Pacane/pacino/variants/insert_test.3mf

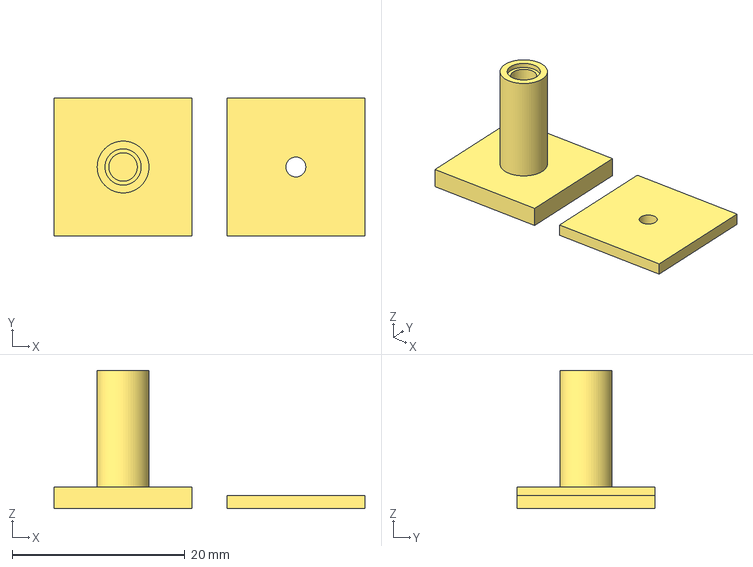
[picture p42: CAD file, 2026-09-14]
variants/insert_test.3mf
36.0 x 16.0 x 16.0 mm
