Pacane/pacino/variants/5col_extra2_bat103450_nodisplay/plate_right.step

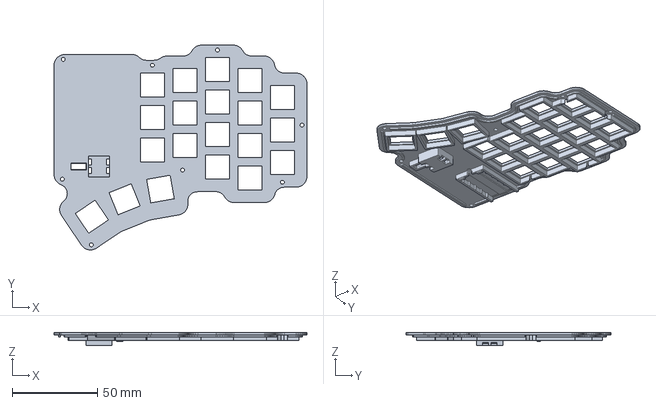
[picture p44: CAD file, 2026-09-14]
variants/5col_extra2_bat103450_nodisplay/plate_right.step
148.3 x 120.1 x 7.50 mm
