Pacane/pacino/variants/5col_extra2_bat303040_pcb_flat/pcb_test.3mf

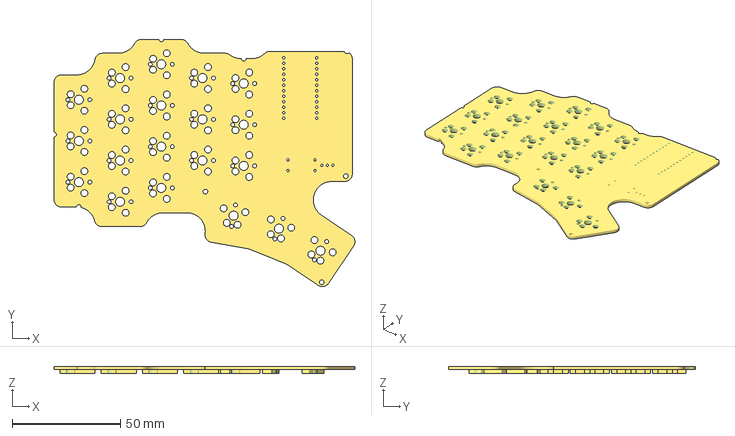
[picture p45: CAD file, 2026-09-14]
variants/5col_extra2_bat303040_pcb_flat/pcb_test.3mf
139.1 x 114.3 x 3.45 mm
