Pacane/pacino/variants/5col_extra2_bat902030_display/plate_right.step

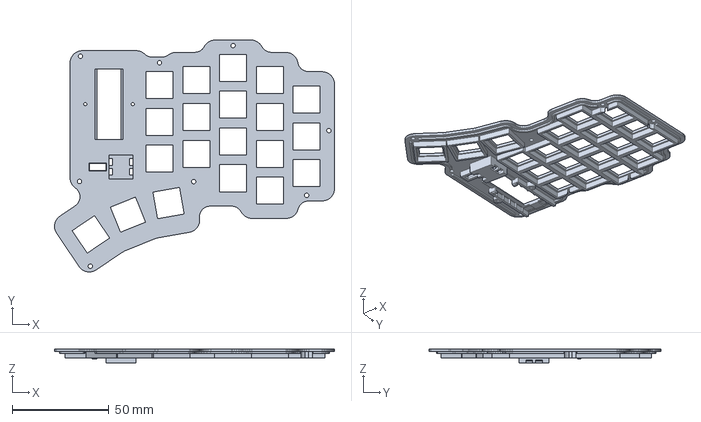
[picture p46: CAD file, 2026-09-14]
variants/5col_extra2_bat902030_display/plate_right.step
144.9 x 120.1 x 7.50 mm
