Pacane/pacino/variants/5col_extra2_bat902030_pcb_pod/plate_left.step

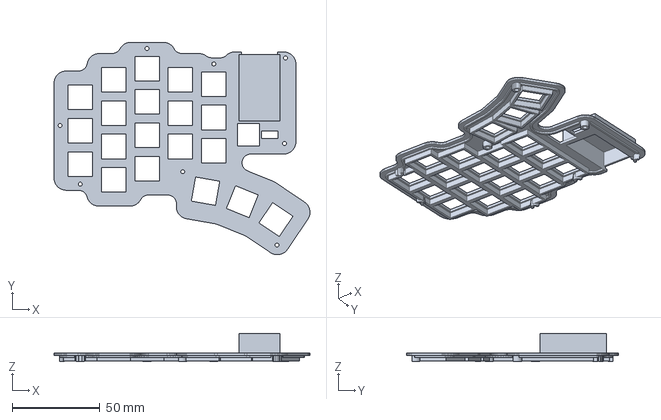
[picture p47: CAD file, 2026-09-14]
variants/5col_extra2_bat902030_pcb_pod/plate_left.step
146.1 x 121.3 x 16.1 mm
