Pacane/pacino/variants/5col_noextra_bat103450_display/bezel_left.step

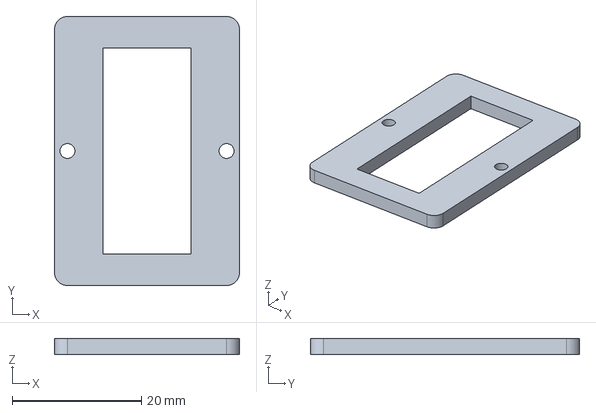
[picture p48: CAD file, 2026-09-14]
variants/5col_noextra_bat103450_display/bezel_left.step
28.6 x 41.6 x 2.50 mm
