Pacane/pacino/variants/5col_noextra_bat103450_nodisplay/plate_left.step

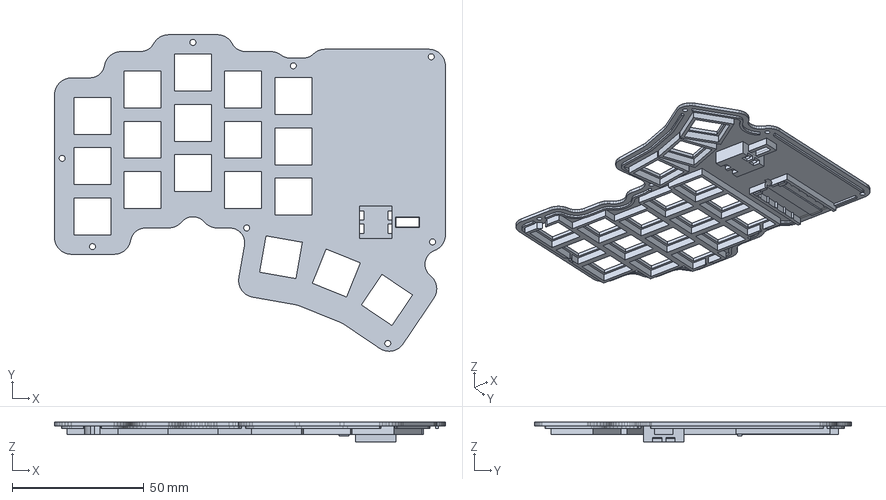
[picture p49: CAD file, 2026-09-14]
variants/5col_noextra_bat103450_nodisplay/plate_left.step
148.3 x 120.1 x 7.50 mm
