Pacane/pacino/variants/5col_noextra_bat902030_nodisplay/plate_right.step

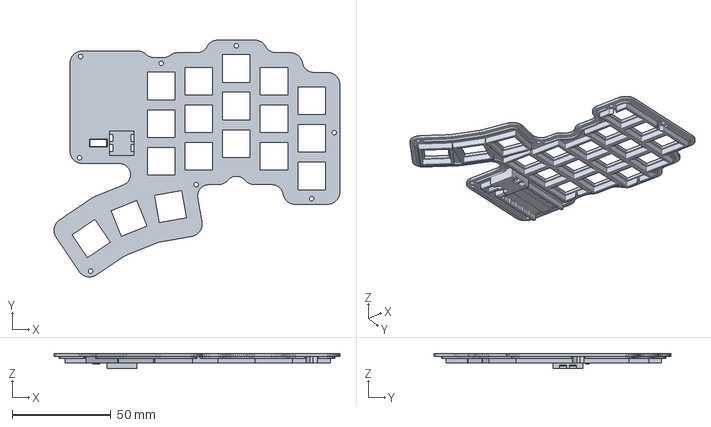
[picture p50: CAD file, 2026-09-14]
variants/5col_noextra_bat902030_nodisplay/plate_right.step
144.9 x 120.1 x 7.50 mm
