Pacane/pacino/variants/6col_extra2_bat902030_display/plate_right.step

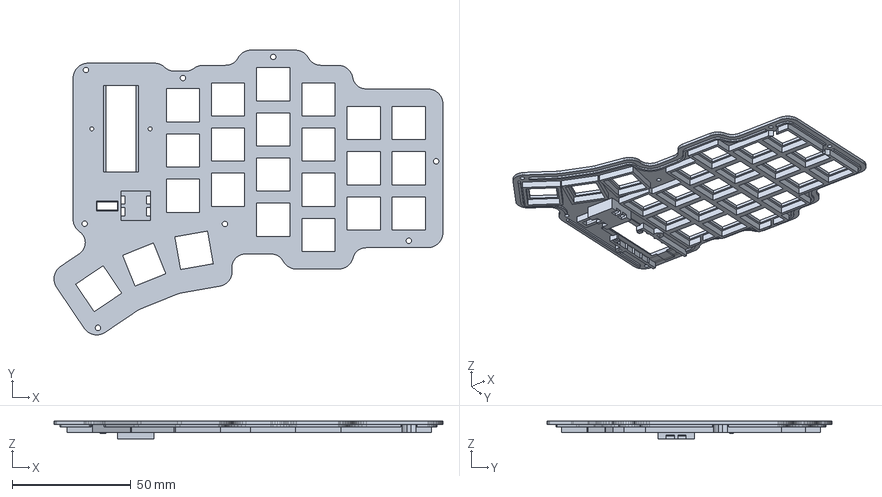
[picture p52: CAD file, 2026-09-14]
variants/6col_extra2_bat902030_display/plate_right.step
164.0 x 120.1 x 7.50 mm
