Pacane/pacino/variants/6col_noextra_bat902030_nodisplay/plate_right.step

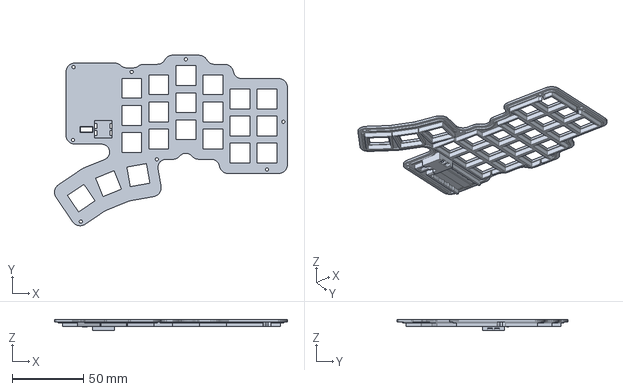
[picture p54: CAD file, 2026-09-14]
variants/6col_noextra_bat902030_nodisplay/plate_right.step
164.0 x 120.1 x 7.50 mm
