Pacane/pacino/variants/5col_extra2_bat303040_pcb_flat/plate_right.step

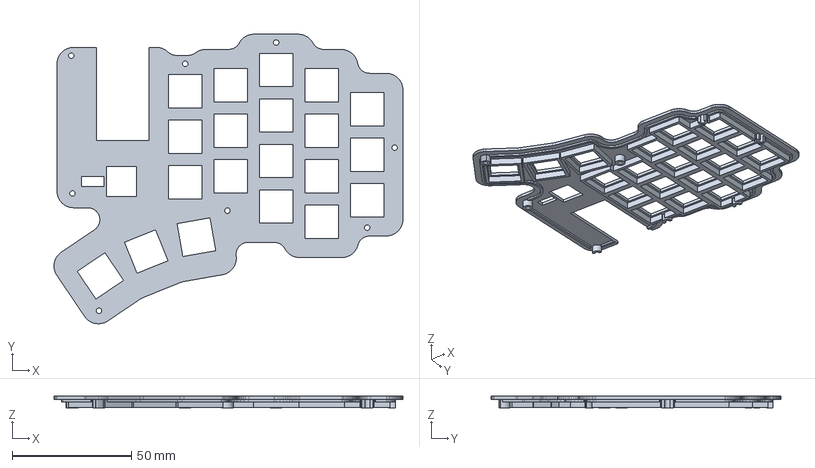
[picture p55: CAD file, 2026-09-14]
variants/5col_extra2_bat303040_pcb_flat/plate_right.step
146.1 x 121.3 x 5.00 mm
