Pacane/pacino/variants/5col_extra2_bat902030_pcb_pod/pcb_test.3mf

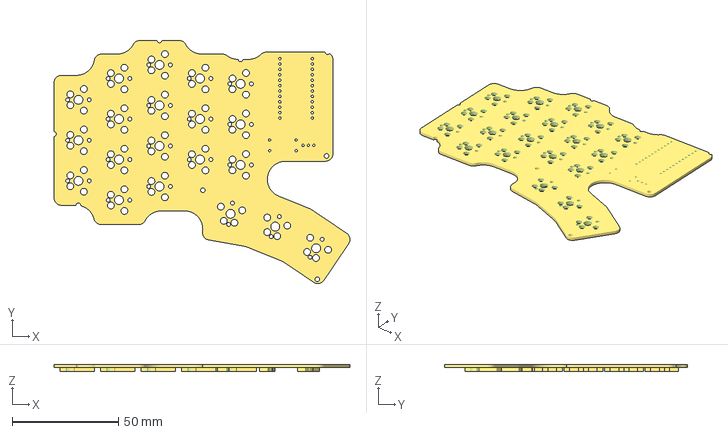
[picture p56: CAD file, 2026-09-14]
variants/5col_extra2_bat902030_pcb_pod/pcb_test.3mf
139.1 x 114.3 x 3.45 mm
