Pacane/pacino/variants/6col_noextra_bat103450_display/plate_left.step

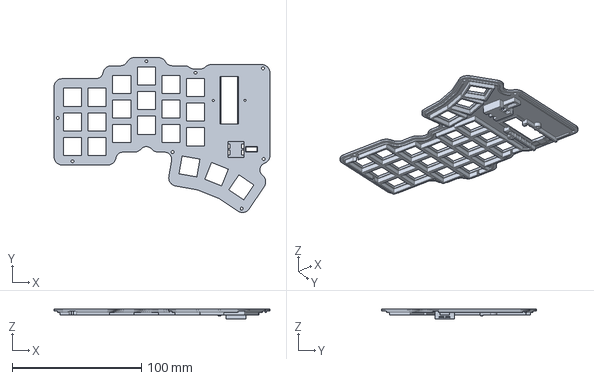
[picture p57: CAD file, 2026-09-14]
variants/6col_noextra_bat103450_display/plate_left.step
167.4 x 120.1 x 7.50 mm
