Pacane/pacino/variants/5col_extra2_bat103450_display/preview_assembly.png

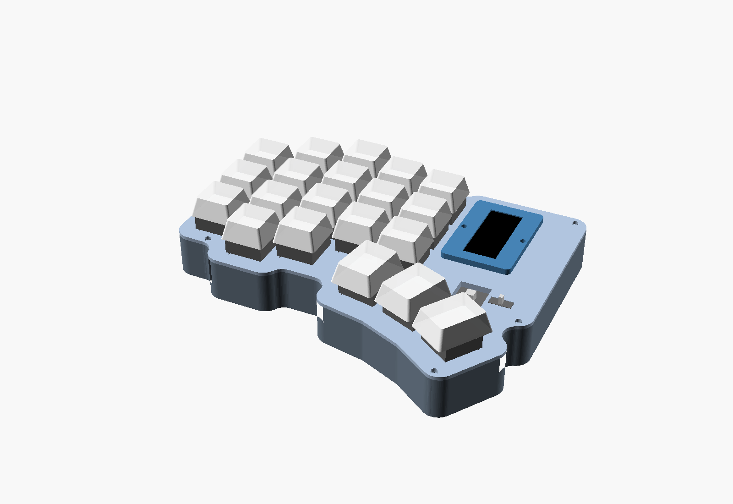
variants/5col_extra2_bat103450_display/preview_assembly.png
