Pacane/pacino/variants/5col_extra2_bat103450_display/wiring_guide.png

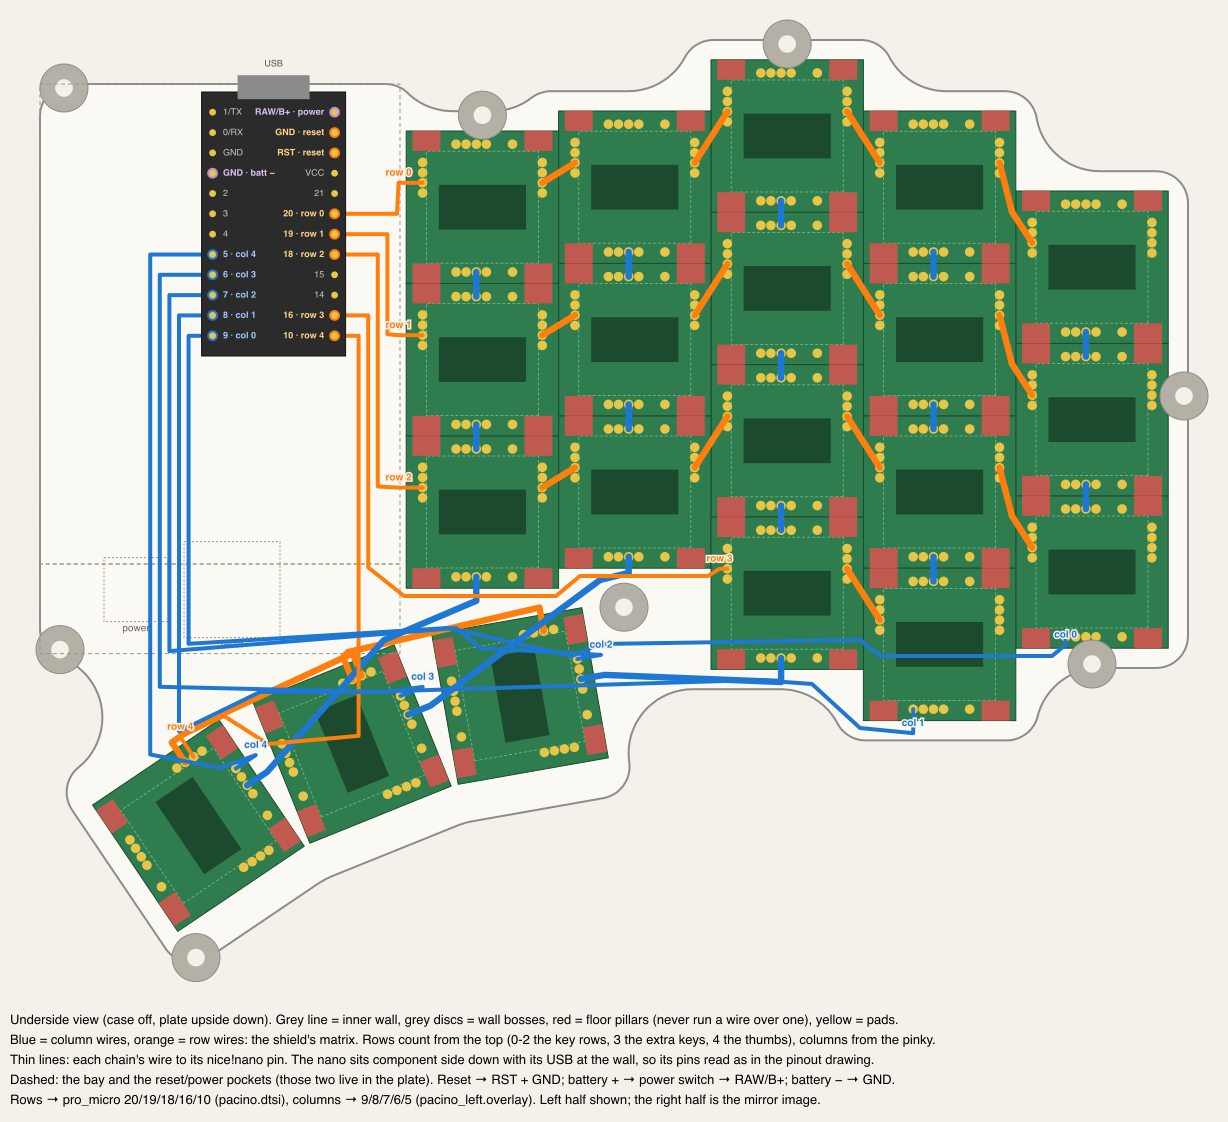
variants/5col_extra2_bat103450_display/wiring_guide.png
