Pacane/pacino/variants/5col_extra2_bat902030_display/preview_assembly.png

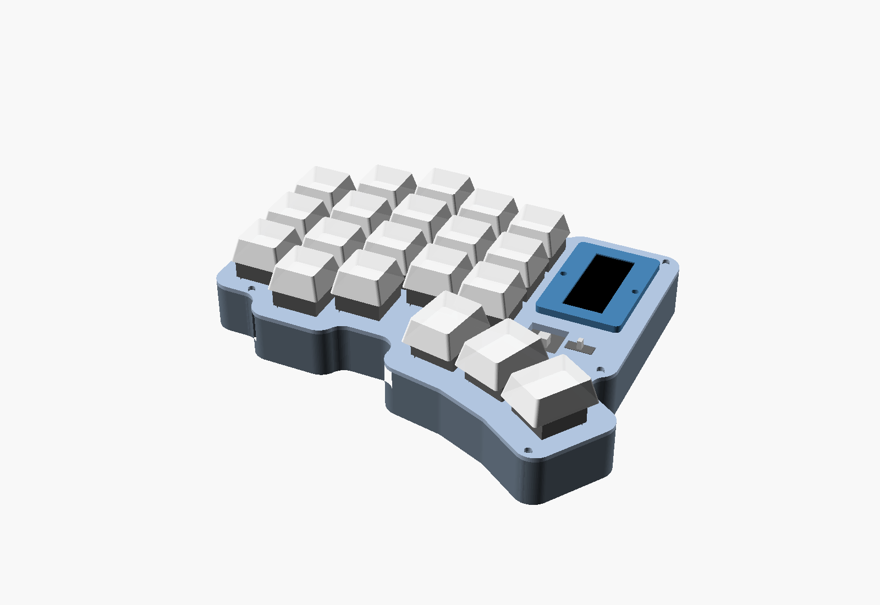
variants/5col_extra2_bat902030_display/preview_assembly.png
