Pacane/pacino/variants/5col_extra2_bat902030_pcb_pod/preview_assembly.png

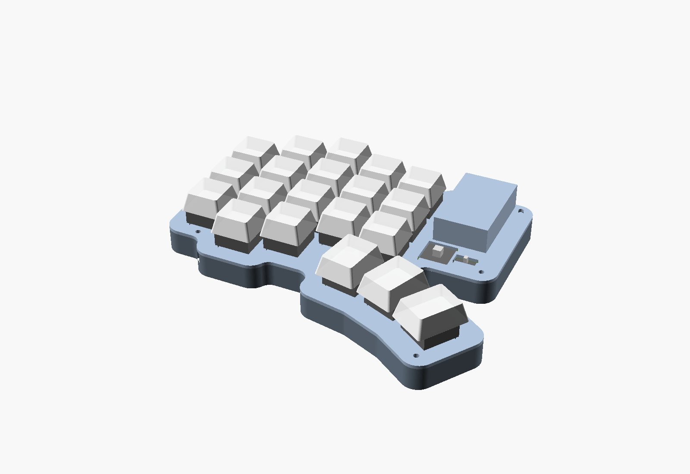
variants/5col_extra2_bat902030_pcb_pod/preview_assembly.png
