Pacane/pacino/variants/6col_extra2_bat103450_display/preview_assembly.png

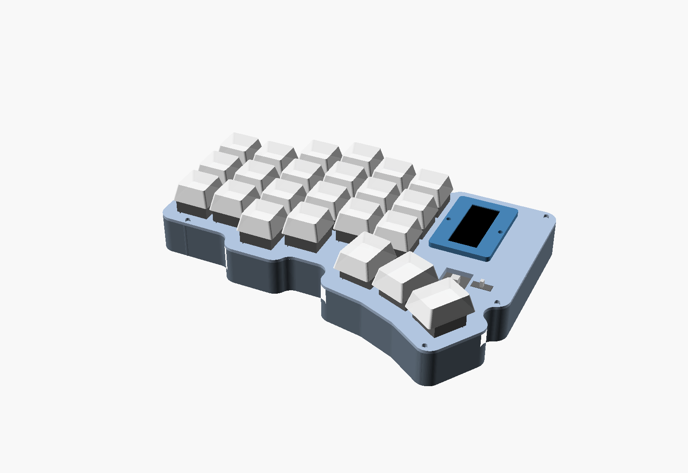
variants/6col_extra2_bat103450_display/preview_assembly.png
