Pacane/pacino/variants/6col_extra2_bat103450_display/wiring_guide.png

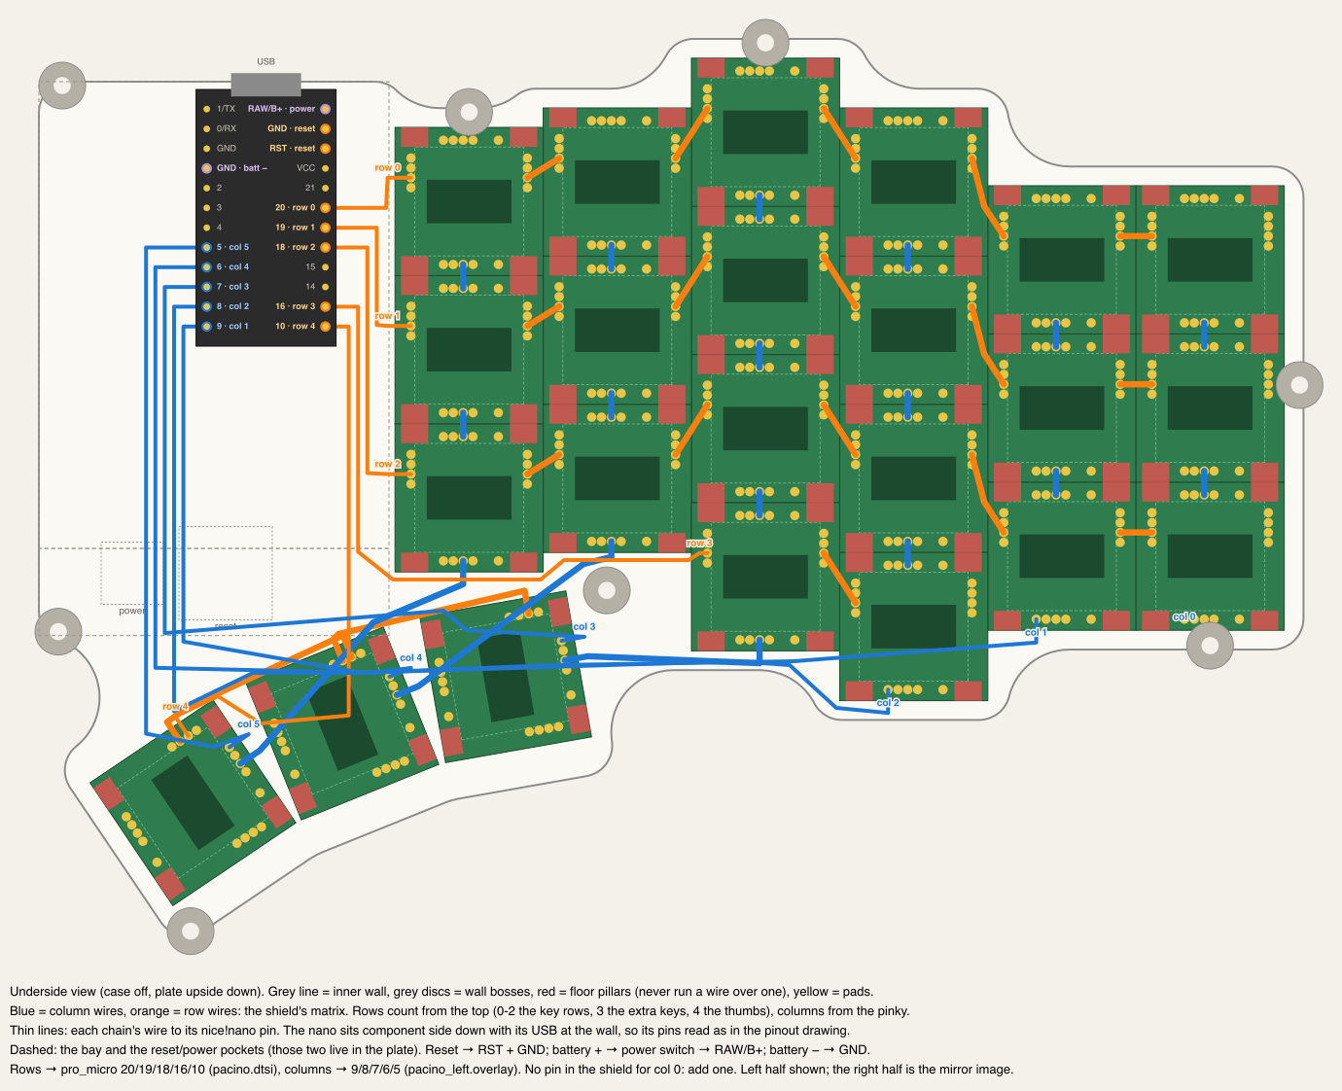
variants/6col_extra2_bat103450_display/wiring_guide.png
