Pacane/pacino/variants/6col_extra2_bat902030_display/wiring_guide.png

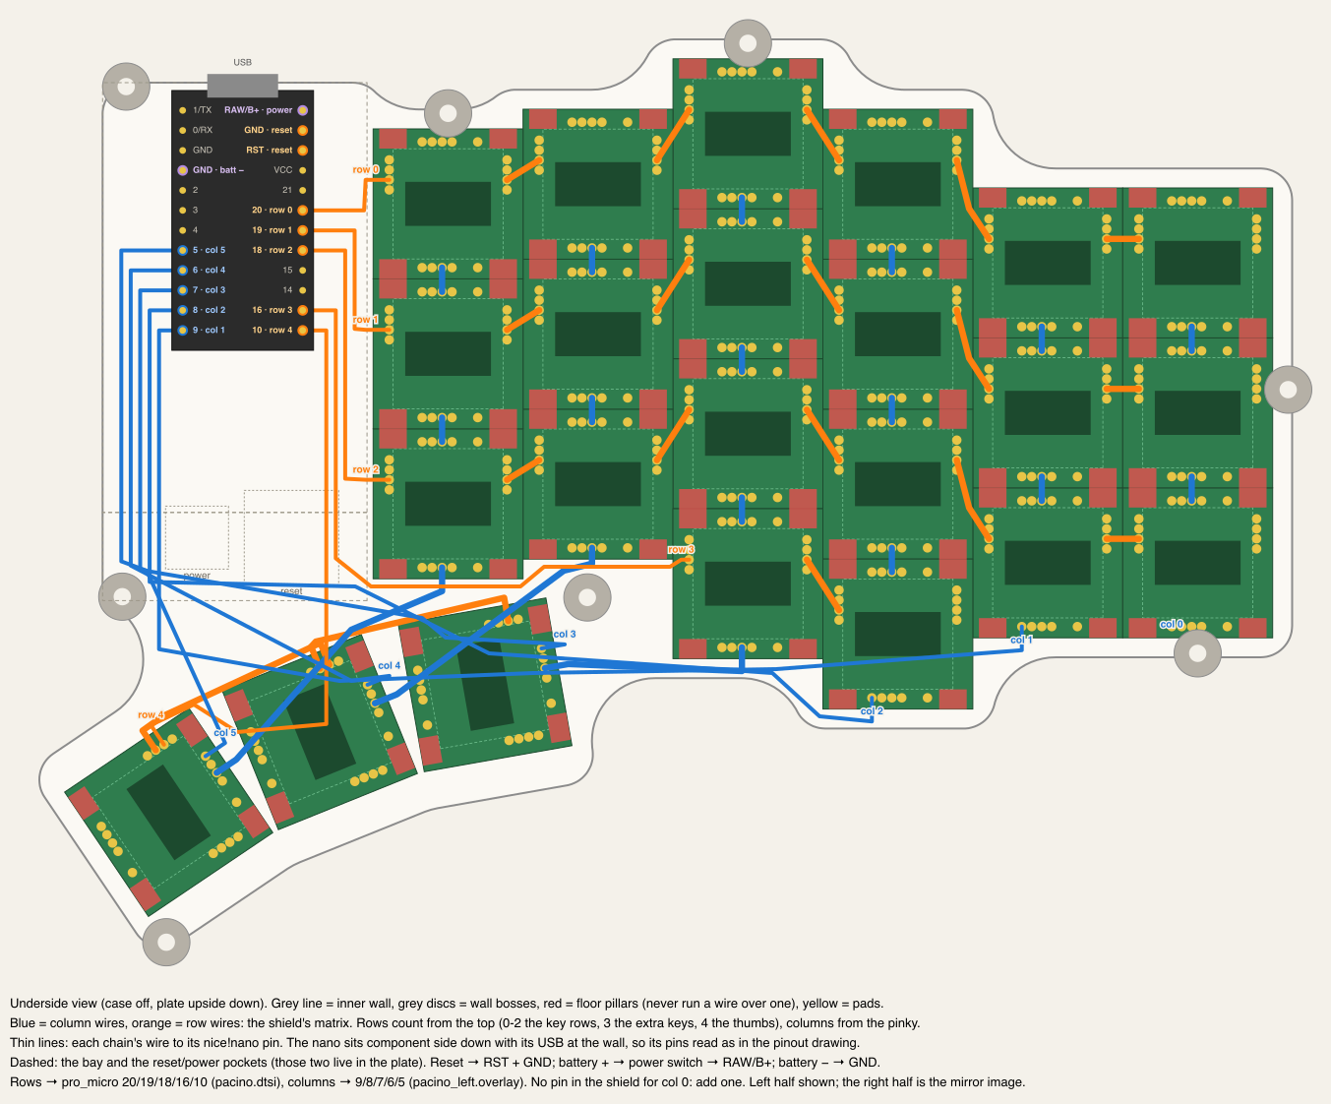
variants/6col_extra2_bat902030_display/wiring_guide.png
