Pacane/pacino/variants/6col_noextra_bat902030_display/wiring_guide.png

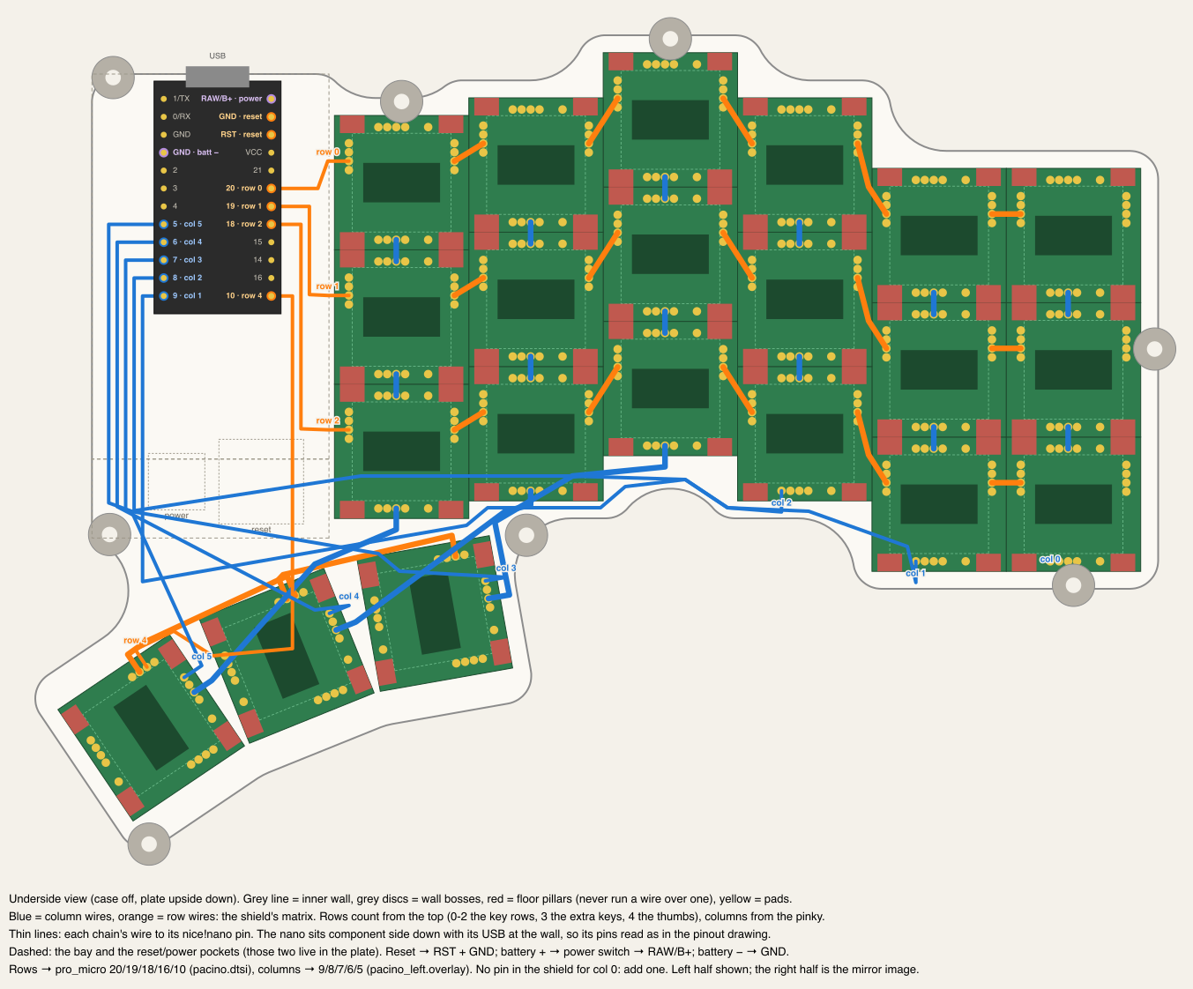
variants/6col_noextra_bat902030_display/wiring_guide.png
